BikeBeamer/BikeBeamer/cad/bikebeamer-v0.2/bikebeamer-v0.1.png

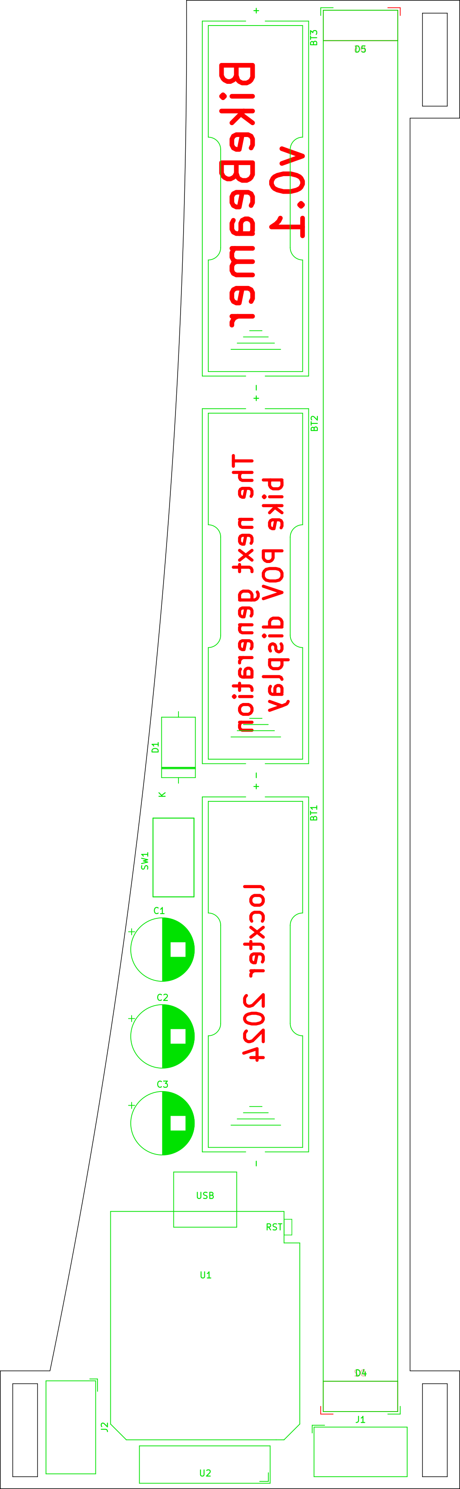
cad/bikebeamer-v0.2/bikebeamer-v0.1.png
