BikeBeamer/BikeBeamer/images/18.png

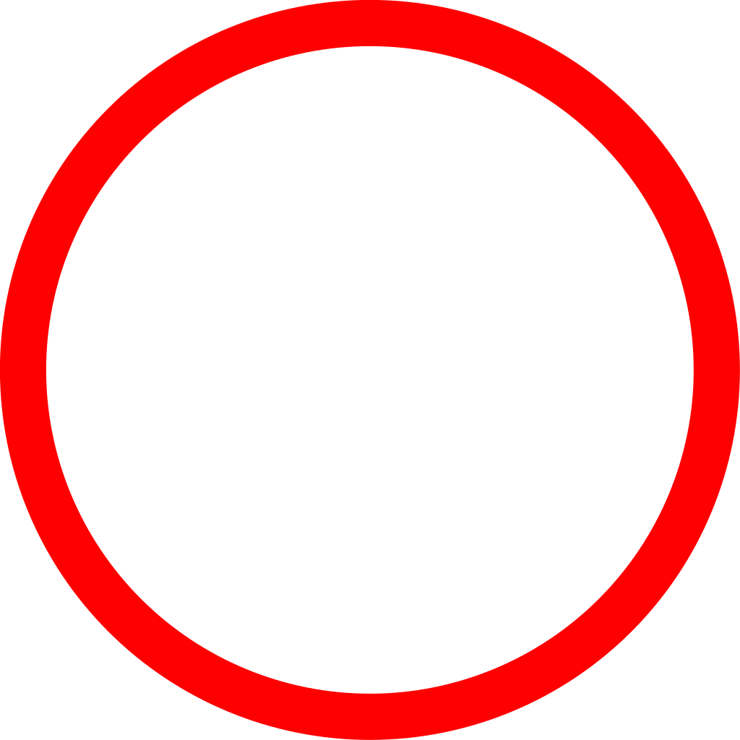
images/18.png
