BikeBeamer/BikeBeamer/images/batman.png

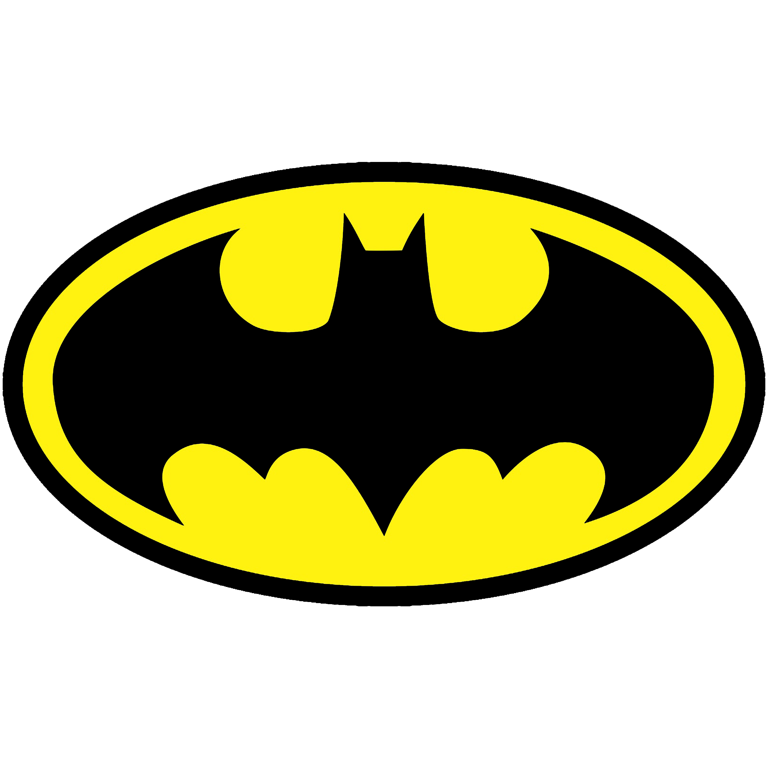
images/batman.png
