BikeBeamer/BikeBeamer/images/green-lantern.png

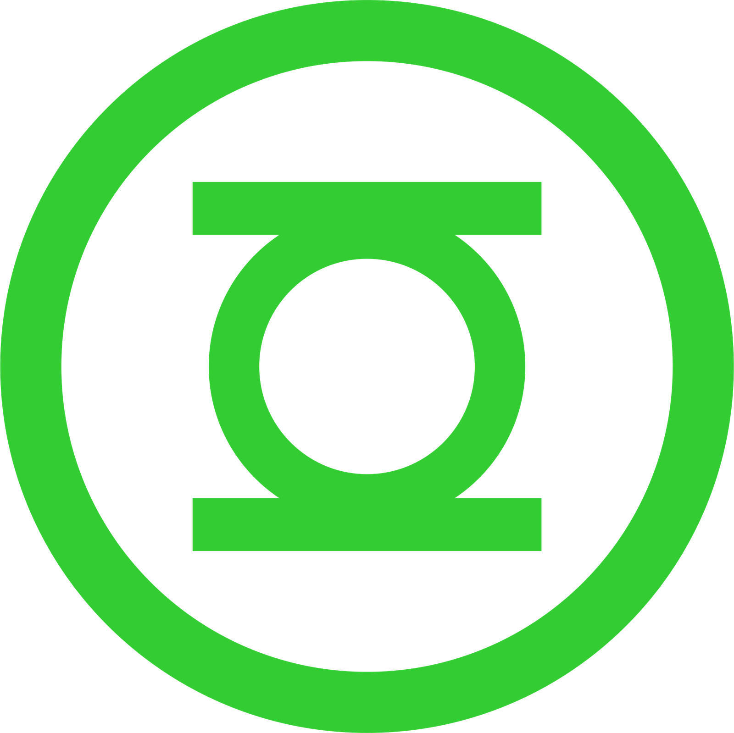
images/green-lantern.png
