BikeBeamer/BikeBeamer/images/tux.png

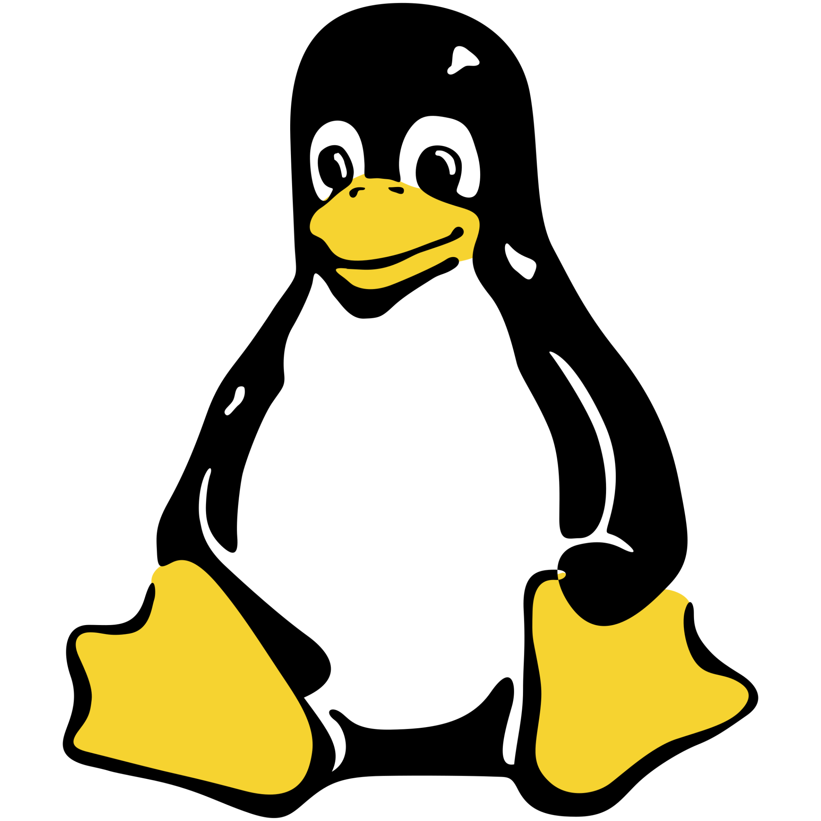
images/tux.png
