BikeBeamer/BikeBeamer/images/wonder-woman.png

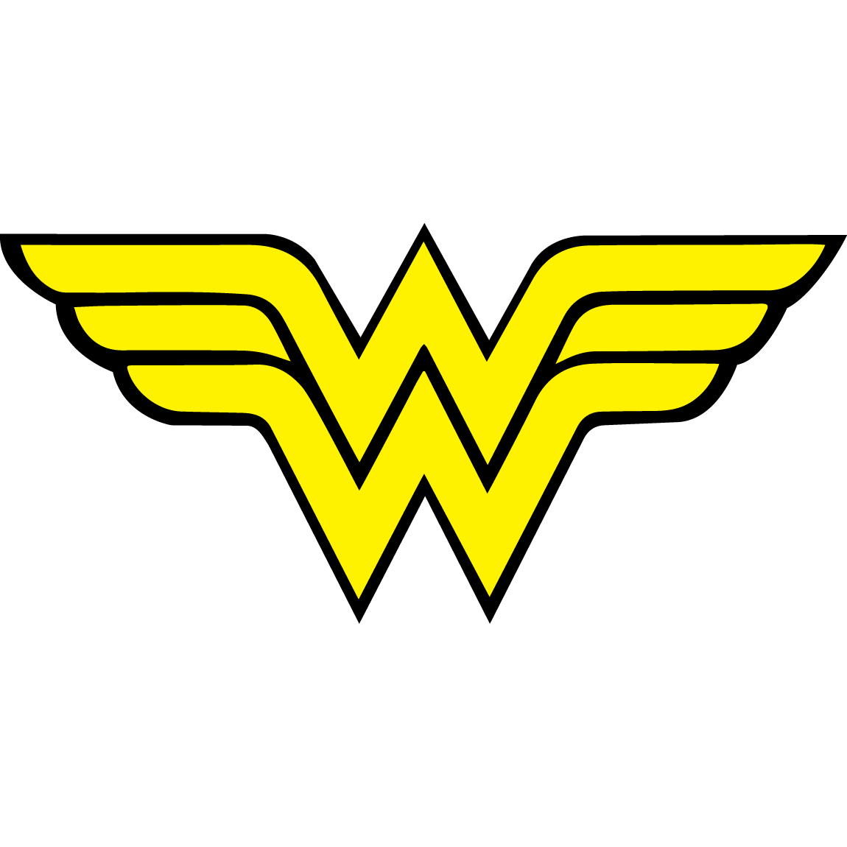
images/wonder-woman.png
